Gabouin/APX_DEVBOARD/images/Capture d'écran 2026-05-12 010754.png

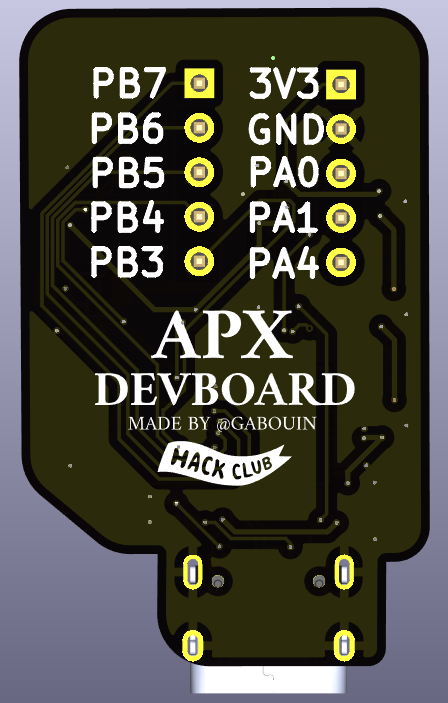
images/Capture d'écran 2026-05-12 010754.png
